Ralakus/tritium/kicad/logic/analog_consensus/consensus.kicad_sch

## KiCad design kicad/logic/analog_consensus/consensus.kicad_sch (2022-08-08)

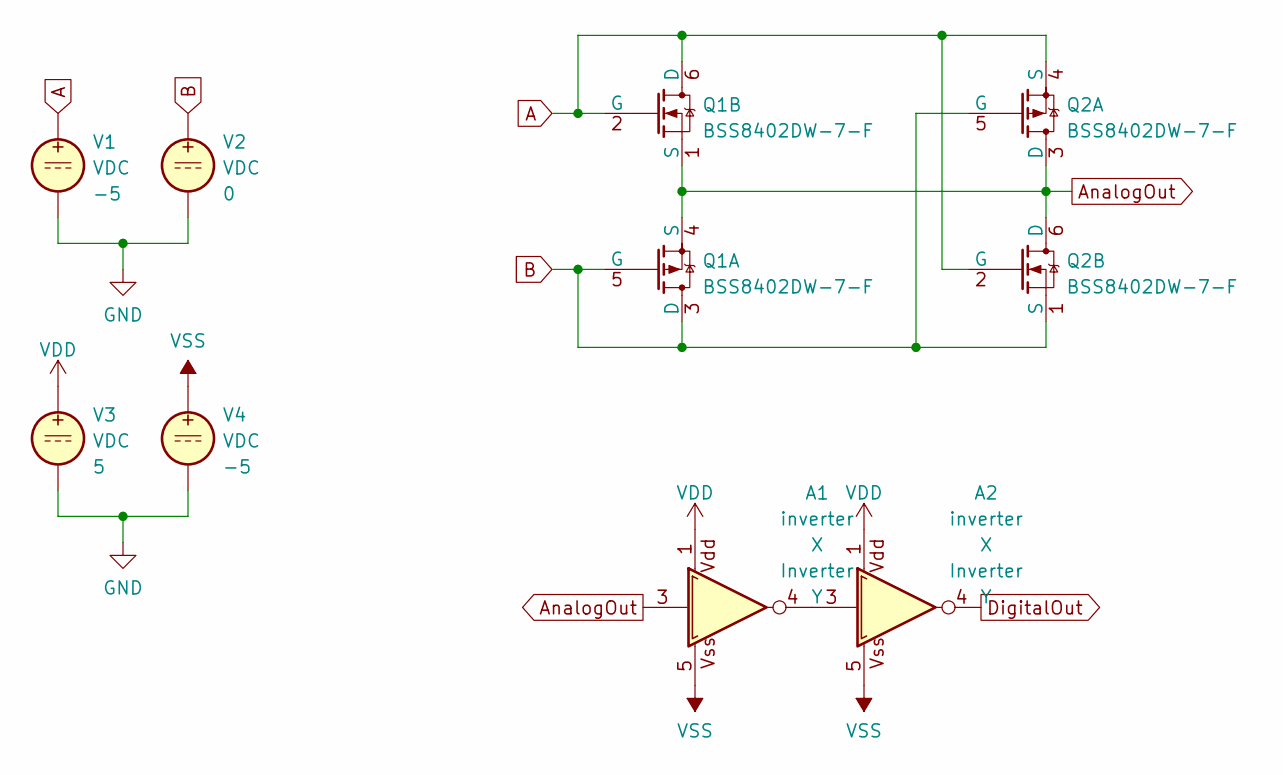
[picture p9: schematic consensus.kicad_sch]

Parts:
A1, A2: inverter
Q1, Q2: BSS8402DW-7-F; SOT-363_SC-70-6_Handsoldering
V1, V2, V3, V4: VDC

Connections:
A: Q1.2 (G), Q1.6 (D), Q2.2 (G), Q2.4 (S), V1.1
AnalogOut: A1.3, Q1.1 (S), Q1.4 (S), Q2.3 (D), Q2.6 (D)
B: Q1.3 (D), Q1.5 (G), Q2.1 (S), Q2.5 (G), V2.1
DigitalOut: A2.4
GND: V1.2, V2.2, V3.2, V4.2
unnamed: A1.4, A2.3
VDD: A1.1, A2.1, V3.1
VSS: A1.5, A2.5, V4.1
