Ralakus/tritium/kicad/logic/and-or-invert/and-or-invert.kicad_sch

## KiCad design kicad/logic/and-or-invert/and-or-invert.kicad_sch (2023-03-02)

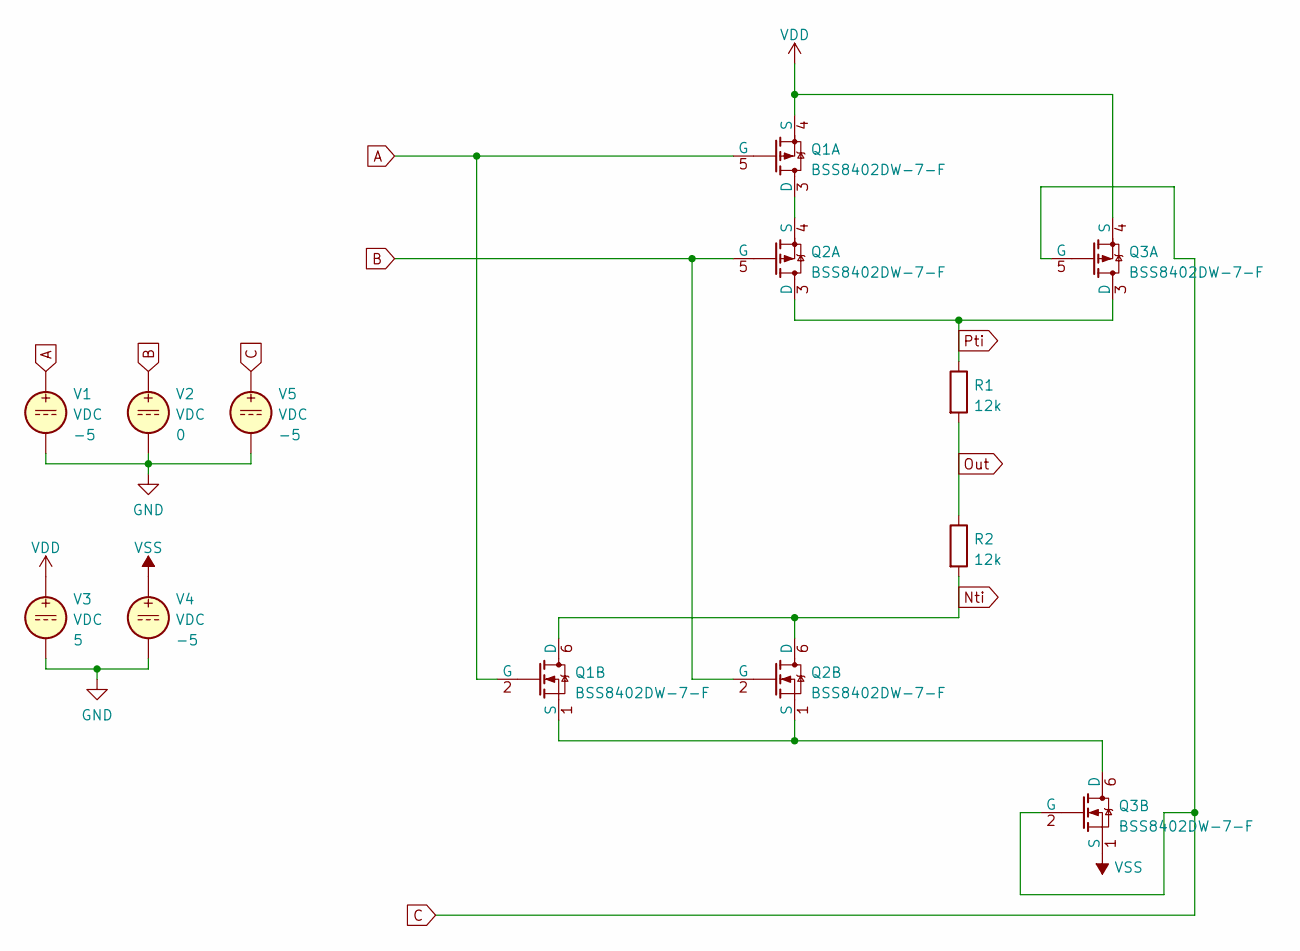
[picture p10: schematic and-or-invert.kicad_sch]

Parts:
Q1, Q2, Q3: BSS8402DW-7-F; SOT-363_SC-70-6_Handsoldering
R1, R2: 12k
V1, V2, V3, V4, V5: VDC

Connections:
A: Q1.2 (G), Q1.5 (G), V1.1
B: Q2.2 (G), Q2.5 (G), V2.1
C: Q3.2 (G), Q3.5 (G), V5.1
GND: V1.2, V2.2, V3.2, V4.2, V5.2
unnamed: Q1.1 (S), Q2.1 (S), Q3.6 (D)
unnamed: Q1.3 (D), Q2.4 (S)
Nti: Q1.6 (D), Q2.6 (D), R2.2
Out: R1.2, R2.1
Pti: Q2.3 (D), Q3.3 (D), R1.1
VDD: Q1.4 (S), Q3.4 (S), V3.1
VSS: Q3.1 (S), V4.1
