Ralakus/tritium/kicad/logic/compare/compare.kicad_sch

## KiCad design kicad/logic/compare/compare.kicad_sch (2023-03-02)

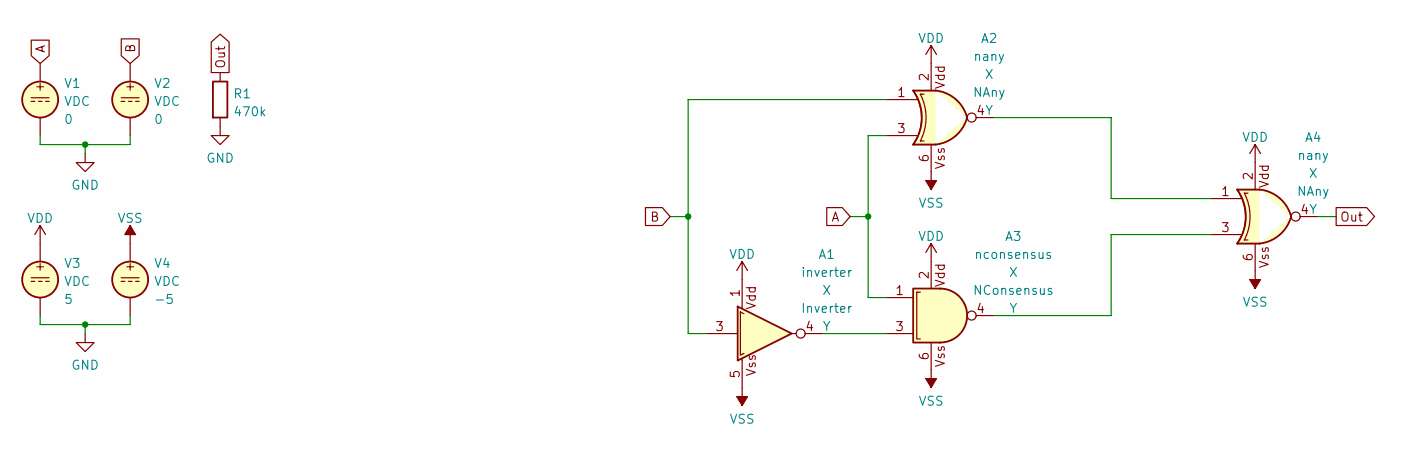
[picture p11: schematic compare.kicad_sch]

Parts:
A1: inverter
A2, A4: nany
A3: nconsensus
R1: 470k
V1, V2, V3, V4: VDC

Connections:
A: A2.3, A3.1, V1.1
B: A1.3, A2.1, V2.1
GND: R1.2, V1.2, V2.2, V3.2, V4.2
unnamed: A1.4, A3.3
unnamed: A2.4, A4.1
unnamed: A3.4, A4.3
Out: A4.4, R1.1
VDD: A1.1, A2.2, A3.2, A4.2, V3.1
VSS: A1.5, A2.6, A3.6, A4.6, V4.1
